twalker/dactyl-keyboard/src/parts/loligaggers_x_2.stl

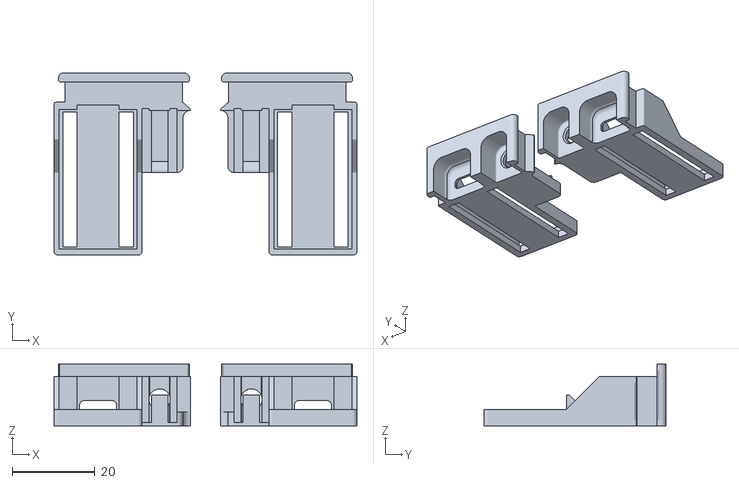
[picture p15: CAD file, 2022-07-11]
src/parts/loligaggers_x_2.stl
73.3 x 44.1 x 15.0
