twalker/dactyl-keyboard/src/parts/hot_swap_wyld.step

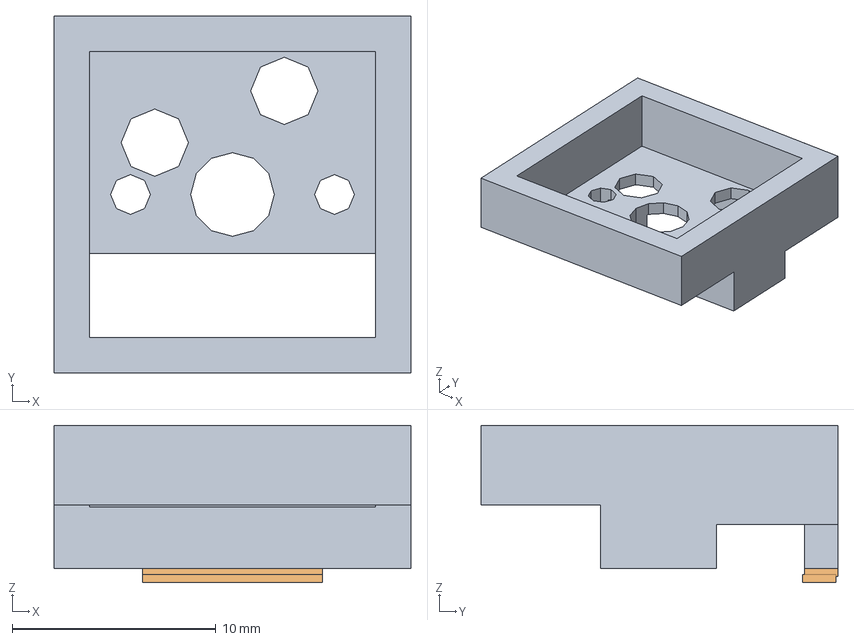
[picture p16: CAD file, 2022-04-22]
src/parts/hot_swap_wyld.step
17.5 x 17.5 x 7.70 mm
