twalker/dactyl-keyboard/src/parts/btu_trackball_socket.step

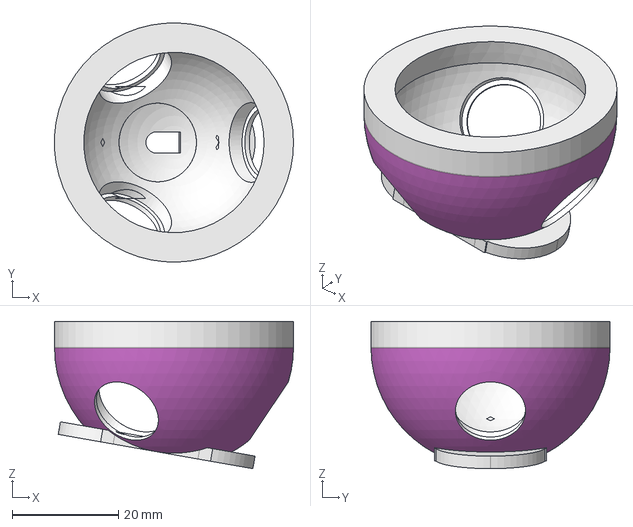
[picture p17: CAD file, 2022-04-07]
src/parts/btu_trackball_socket.step
45.0 x 45.0 x 27.7 mm
