twalker/dactyl-keyboard/src/parts/trackball_socket_w_btus_cutter.step

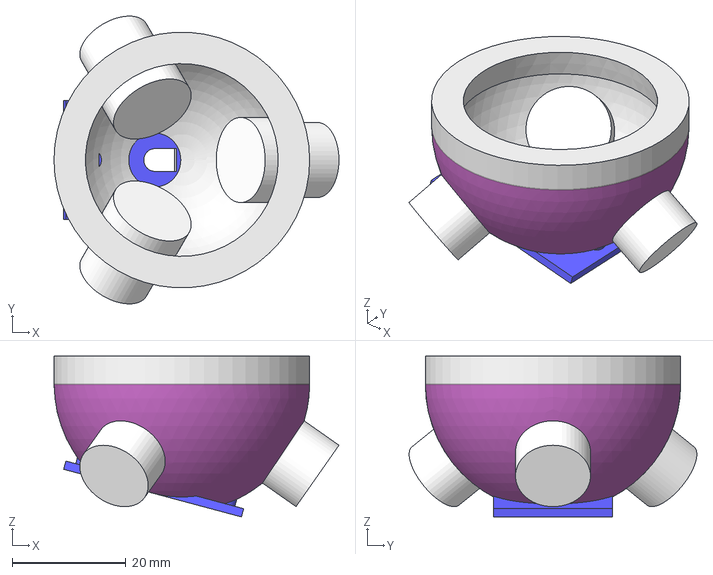
[picture p18: CAD file, 2022-03-27]
src/parts/trackball_socket_w_btus_cutter.step
50.2 x 50.7 x 28.3 mm
