twalker/dactyl-keyboard/src/parts/trackball_socket_btu.step

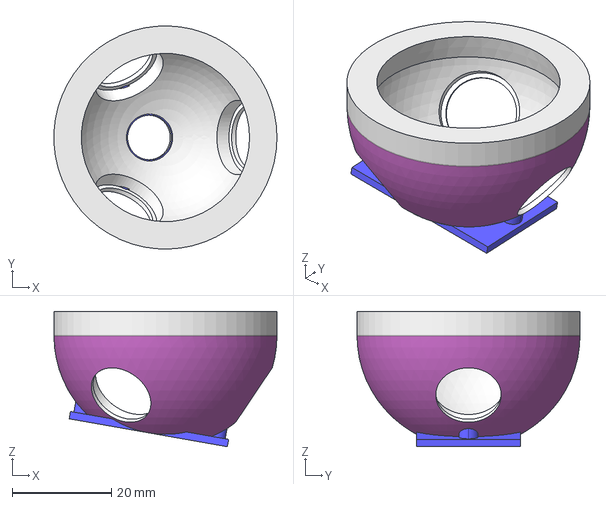
[picture p19: CAD file, 2022-03-27]
src/parts/trackball_socket_btu.step
45.0 x 45.0 x 27.3 mm
