twalker/dactyl-keyboard/src/parts/dactyl_wrist_rest_v3_left.stl

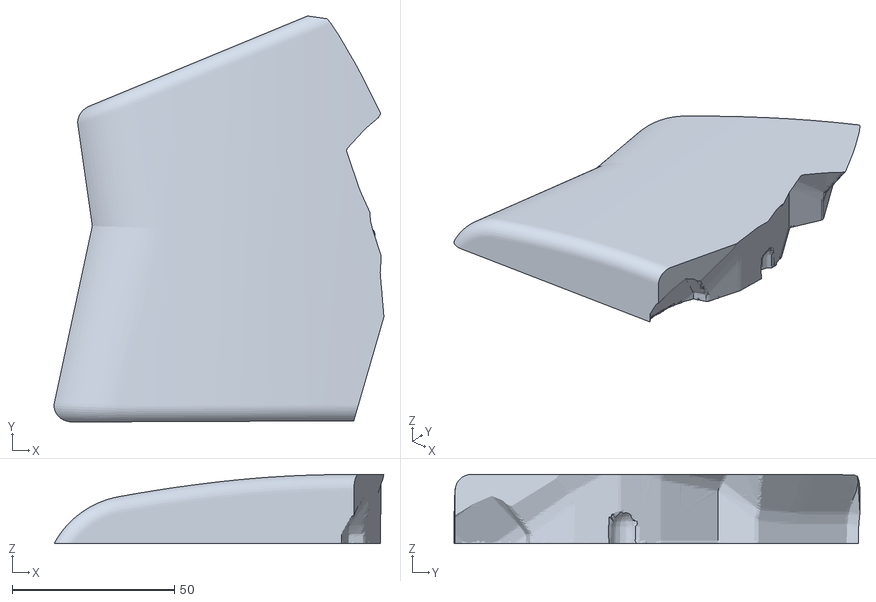
[picture p20: CAD file, 2022-03-15]
src/parts/dactyl_wrist_rest_v3_left.stl
101.7 x 125.2 x 21.4
