twalker/dactyl-keyboard/src/parts/hotswap_ridged_test_notched.stl

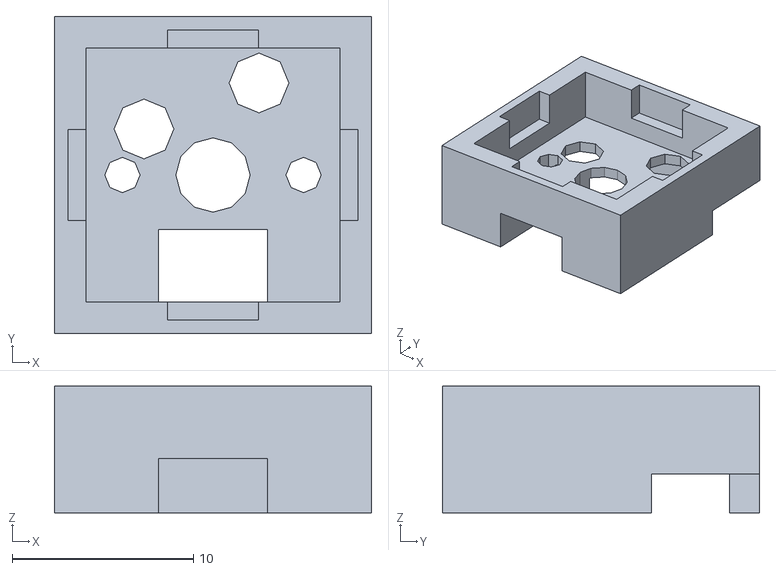
[picture p21: CAD file, 2022-03-02]
src/parts/hotswap_ridged_test_notched.stl
17.5 x 17.5 x 7.00
