twalker/dactyl-keyboard/src/parts/hotswap_ridged_test.step

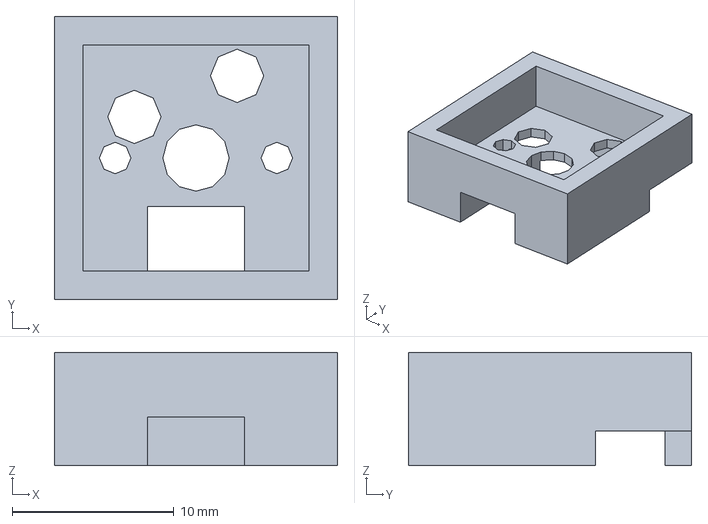
[picture p22: CAD file, 2022-03-02]
src/parts/hotswap_ridged_test.step
17.5 x 17.5 x 7.00 mm
