twalker/dactyl-keyboard/src/parts/derek_hotswap.stl

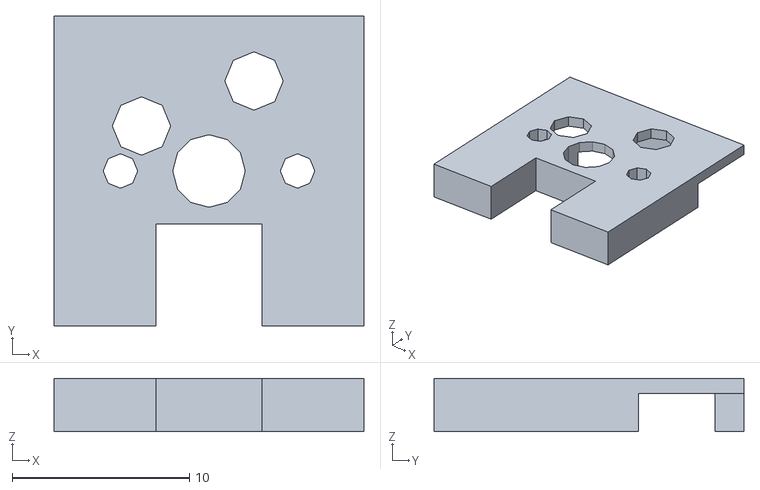
[picture p23: CAD file, 2021-11-29]
src/parts/derek_hotswap.stl
17.5 x 17.5 x 3.00
